crls-design/A7-Minima/vivado/led_demo/led_demo.srcs/sources_1/new/sin_lut.v

module sin_lut (
    input [7:0] PHASE,
    output reg [7:0] VALUE
);

    always @(*) begin
        case (PHASE)
            8'd0:   VALUE = 8'd128;
            8'd1:   VALUE = 8'd131;
            8'd2:   VALUE = 8'd134;
            8'd3:   VALUE = 8'd137;
            8'd4:   VALUE = 8'd140;
            8'd5:   VALUE = 8'd143;
            8'd6:   VALUE = 8'd146;
            8'd7:   VALUE = 8'd149;
            8'd8:   VALUE = 8'd152;
            8'd9:   VALUE = 8'd156;
            8'd10:  VALUE = 8'd159;
            8'd11:  VALUE = 8'd162;
            8'd12:  VALUE = 8'd165;
            8'd13:  VALUE = 8'd168;
            8'd14:  VALUE = 8'd171;
            8'd15:  VALUE = 8'd174;
            8'd16:  VALUE = 8'd176;
            8'd17:  VALUE = 8'd179;
            8'd18:  VALUE = 8'd182;
            8'd19:  VALUE = 8'd185;
            8'd20:  VALUE = 8'd188;
            8'd21:  VALUE = 8'd191;
            8'd22:  VALUE = 8'd193;
            8'd23:  VALUE = 8'd196;
            8'd24:  VALUE = 8'd199;
            8'd25:  VALUE = 8'd201;
            8'd26:  VALUE = 8'd204;
            8'd27:  VALUE = 8'd206;
            8'd28:  VALUE = 8'd209;
            8'd29:  VALUE = 8'd211;
            8'd30:  VALUE = 8'd213;
            8'd31:  VALUE = 8'd216;
            8'd32:  VALUE = 8'd218;
            8'd33:  VALUE = 8'd220;
            8'd34:  VALUE = 8'd222;
            8'd35:  VALUE = 8'd224;
            8'd36:  VALUE = 8'd226;
            8'd37:  VALUE = 8'd228;
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
            8'd242: VALUE = 8'd87;
            8'd243: VALUE = 8'd90;
            8'd244: VALUE = 8'd93;
            8'd245: VALUE = 8'd96;
            8'd246: VALUE = 8'd99;
            8'd247: VALUE = 8'd103;
            8'd248: VALUE = 8'd106;
            8'd249: VALUE = 8'd109;
            8'd250: VALUE = 8'd112;
            8'd251: VALUE = 8'd115;
            8'd252: VALUE = 8'd118;
            8'd253: VALUE = 8'd121;
            8'd254: VALUE = 8'd124;
            8'd255: VALUE = 8'd127;
        endcase
    end

endmodule
